prozessorkern/LedPixel/stm32f030/pcb/led_pixel_stm32f030/doc/led_pixel_stm32f030.pdf

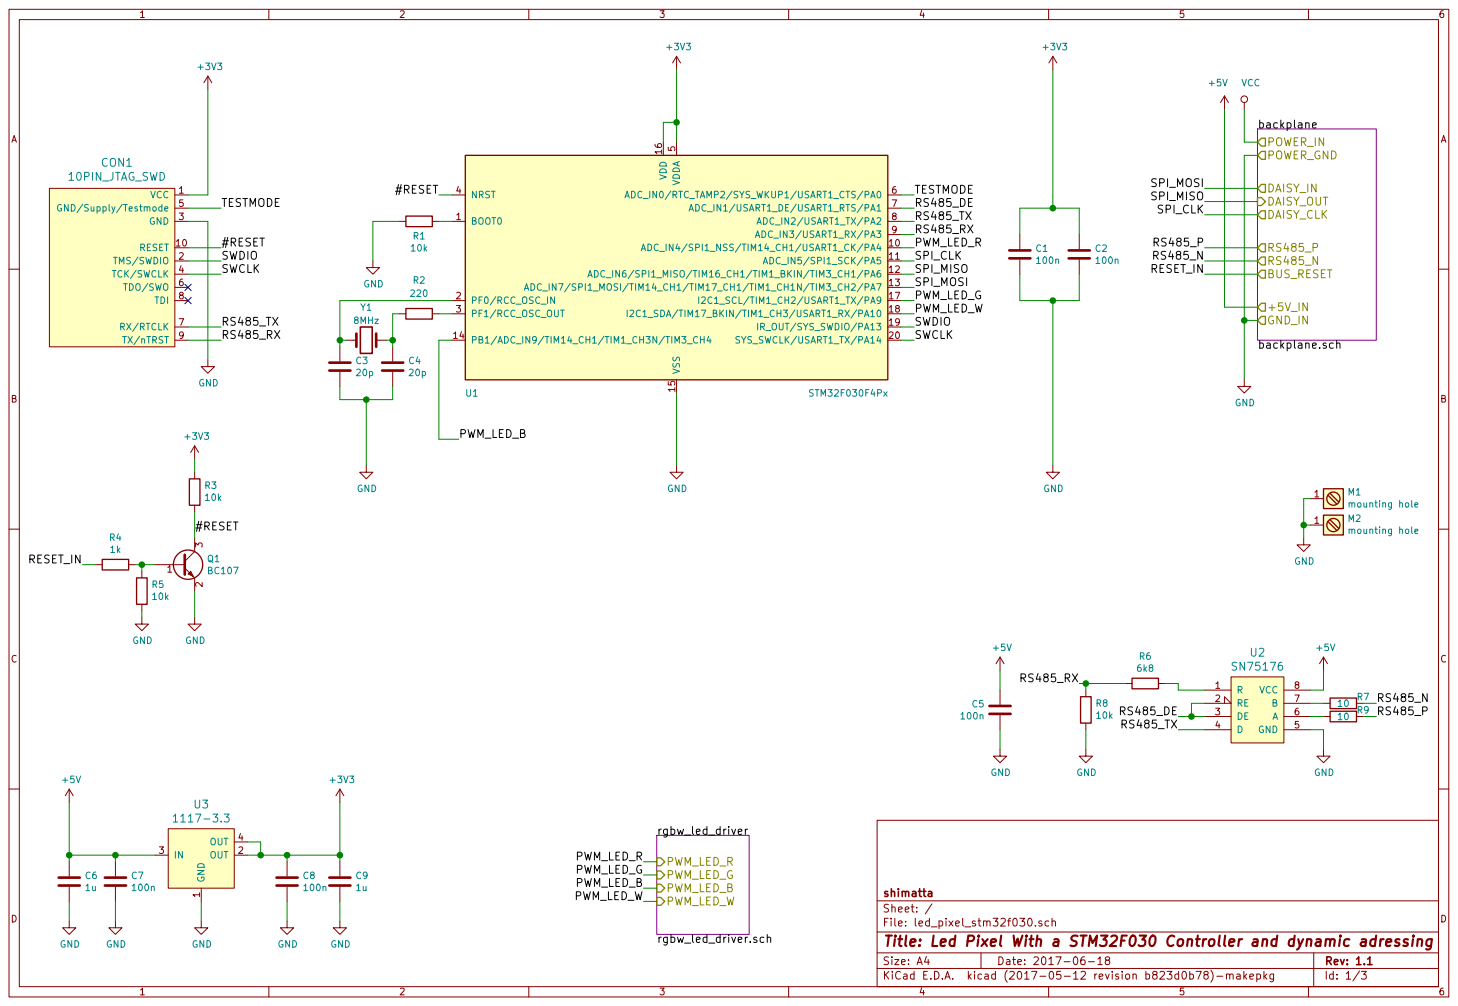
[picture p6: page 1]

File: led_pixel_stm32f030.sch Sheet: / shimatta C7

Id: 1/3 Title: Led Pixel With a STM32F030 Controller and dynamic adressing

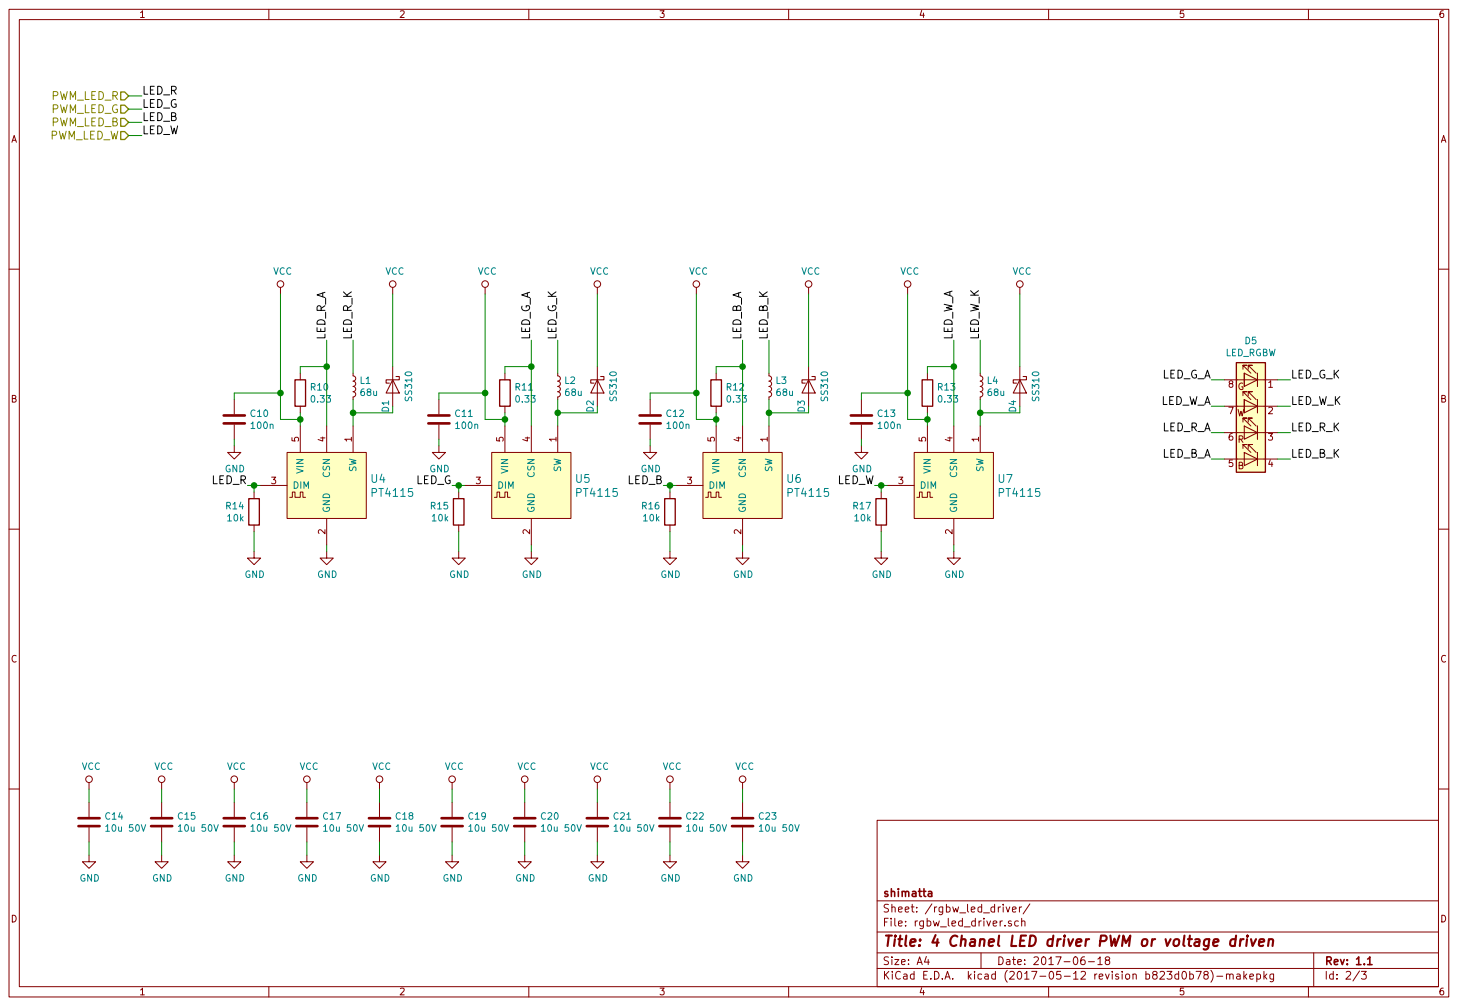
[picture p7: page 2]

File: rgbw_led_driver.sch
Id: 2/3 Title: 4 Chanel LED driver PWM or voltage driven

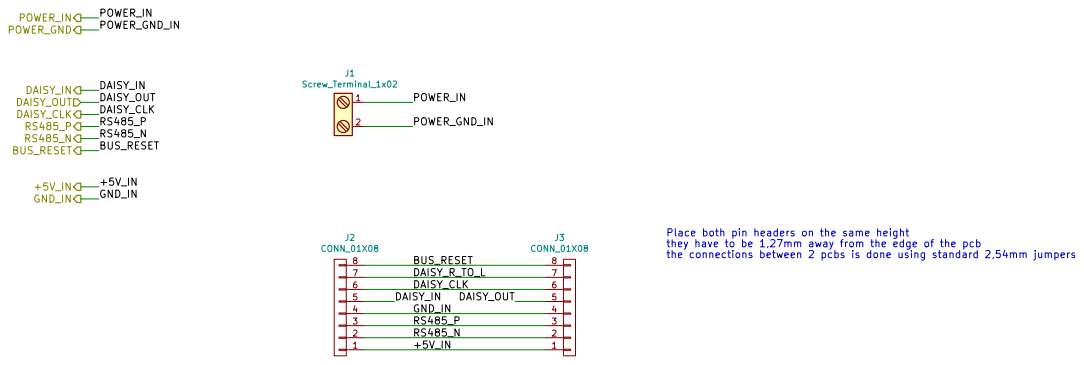
[picture p8: page 3]

Place both pin headers on the same height
they have to be 1,27mm away from the edge of the pcb
the connections between 2 pcbs is done using standard 2,54mm jumpers

File: backplane.sch
Id: 3/3 Title: Led Pixel Backplane connection
