prozessorkern/LedPixel/atmega8/pcb/led_pixel/doc/led_pixel.pdf

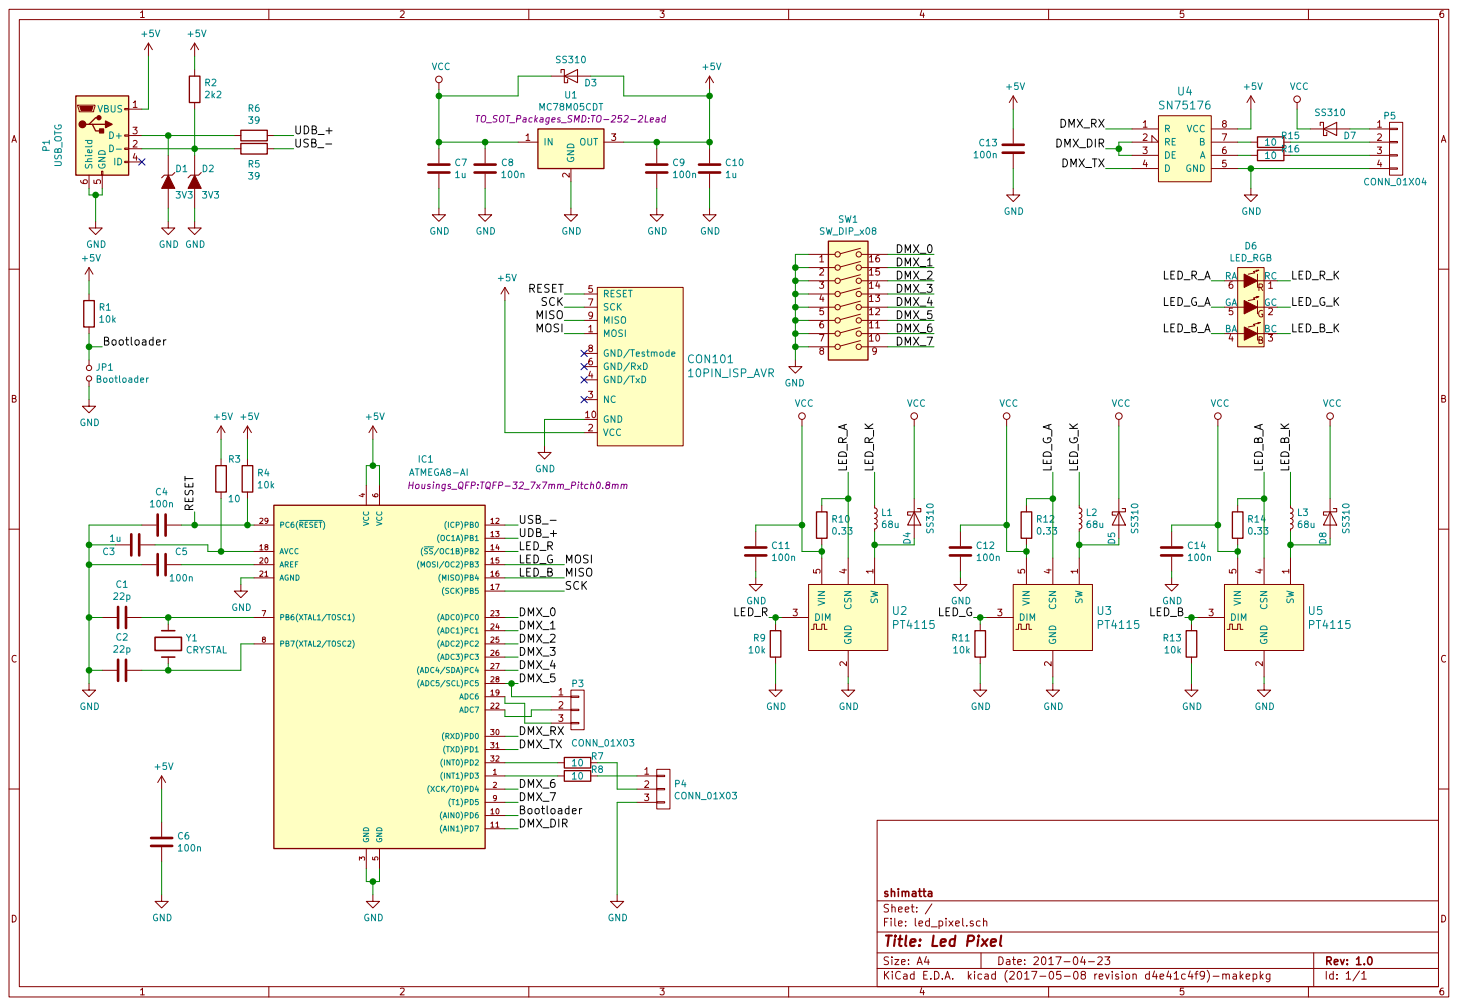
[picture p9: page 1]

UDB_+ Bootloader Bootloader JP1 Bootloader GND

File: led_pixel.sch Sheet: / shimatta

Id: 1/1 Title: Led Pixel
