prozessorkern/LedPixel/stm32f030/pcb/led_pixel_stm32f030/x4/doc/led_pixel_stm32f030_x4-B_SilkS.pdf

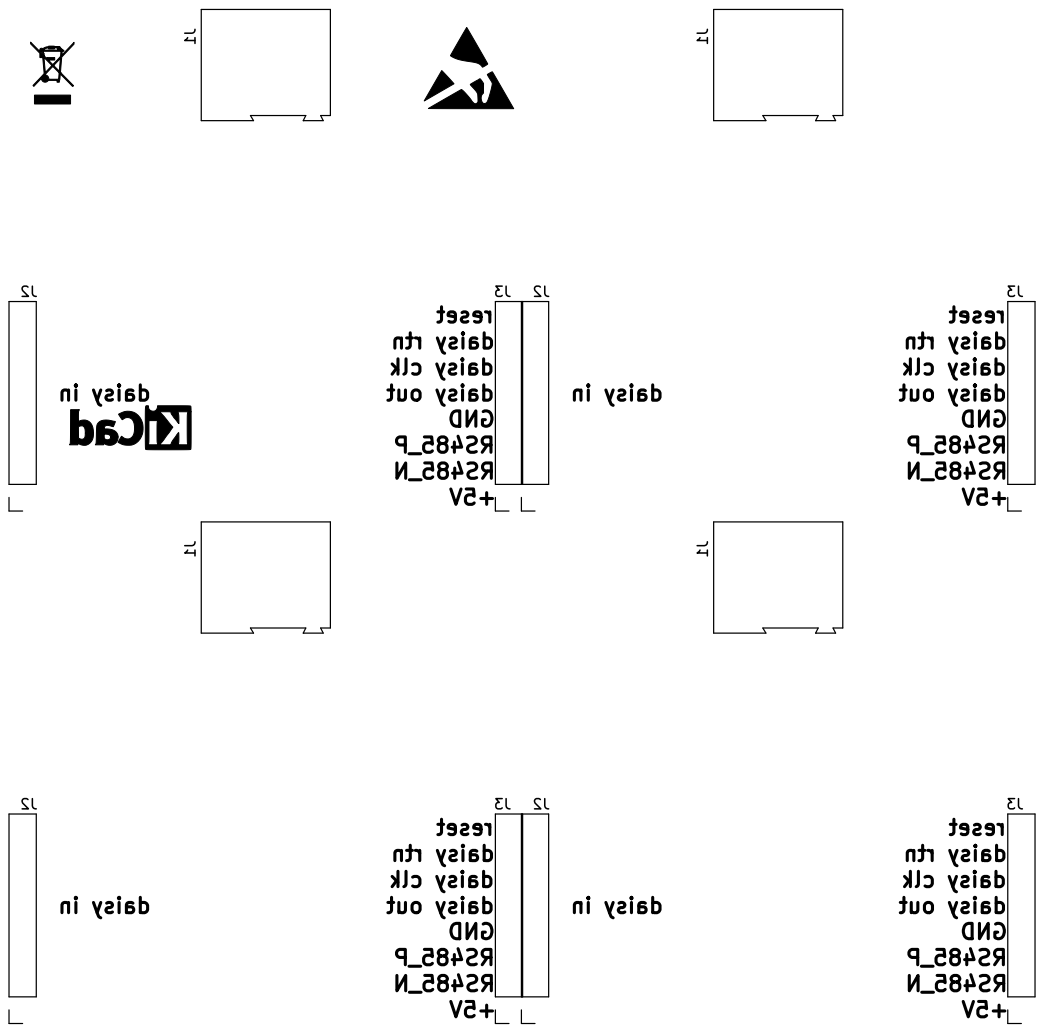
[picture p10: page 1]

daisy out daisy out +5V RS485_N

daisy out reset daisy rtn
