prozessorkern/LedPixel/stm32f030/pcb/led_pixel_stm32f030/doc/led_pixel_stm32f030-B.Cu.pdf

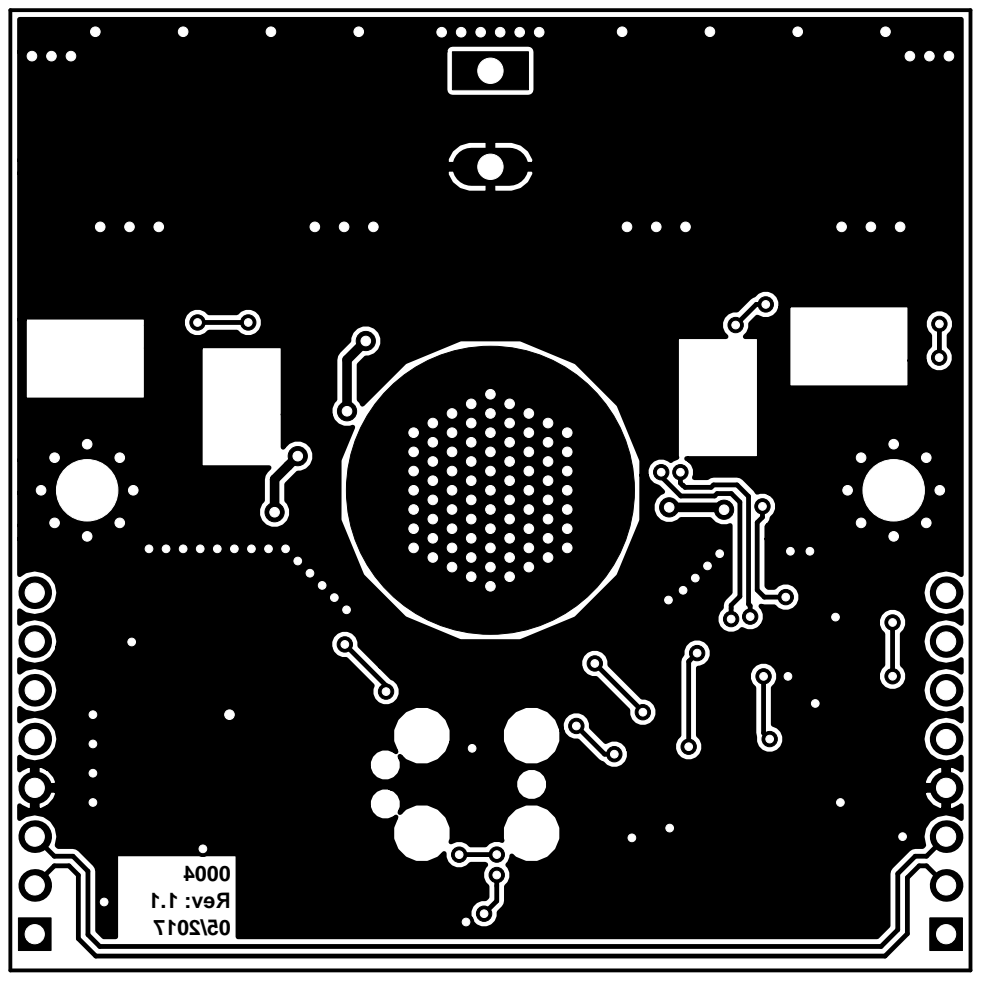
[picture p20: page 1]
