prozessorkern/LedPixel/stm32f030/pcb/led_pixel_stm32f030/doc/led_pixel_stm32f030-B.Mask.pdf

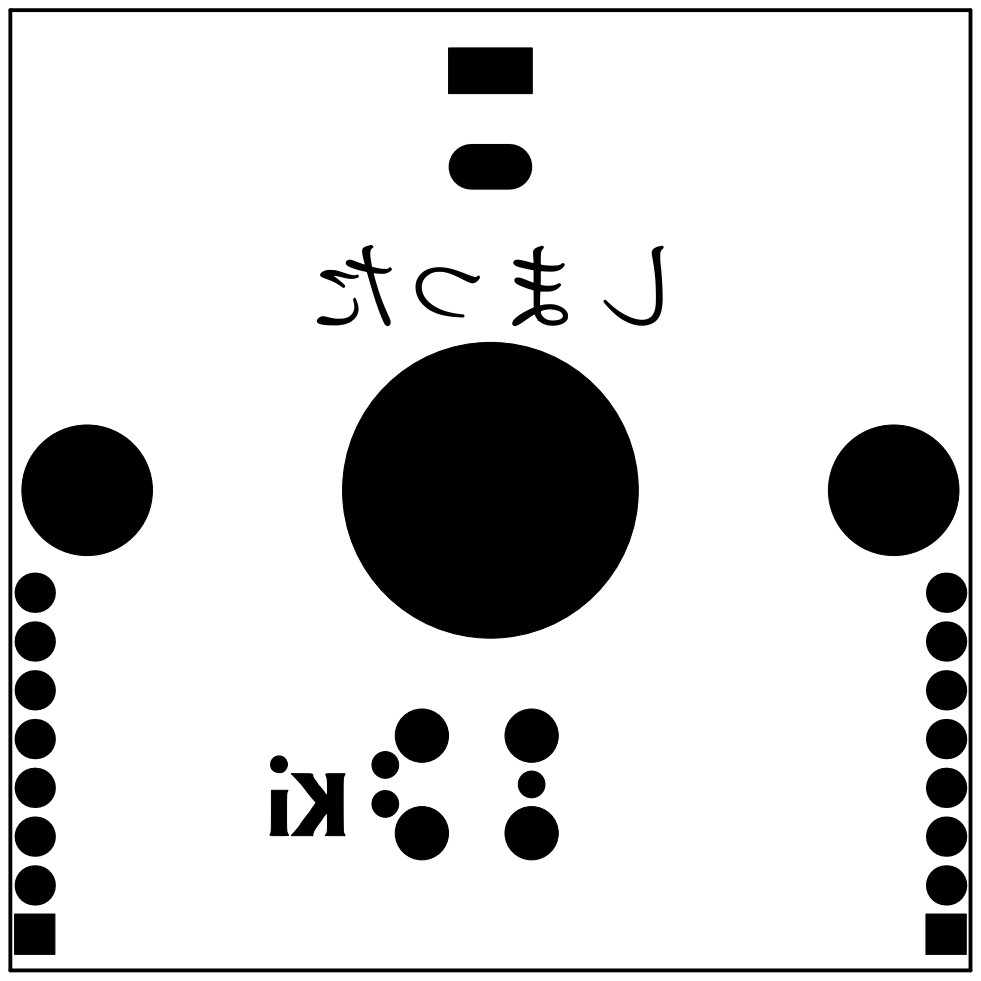
[picture p21: page 1]
