prozessorkern/LedPixel/stm32f030/pcb/led_pixel_stm32f030/doc/led_pixel_stm32f030-B.SilkS.pdf

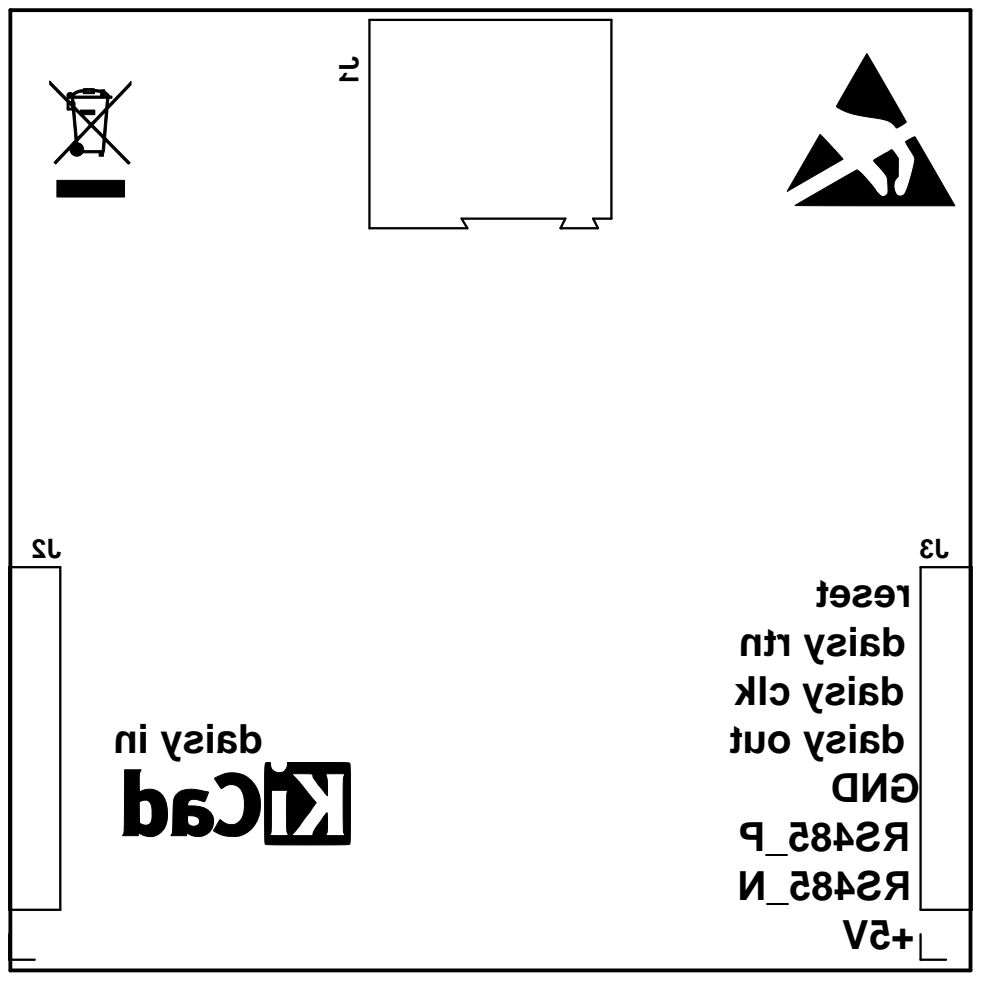
[picture p22: page 1]
