prozessorkern/LedPixel/stm32f030/pcb/led_pixel_stm32f030/doc/led_pixel_stm32f030-F.Cu.pdf

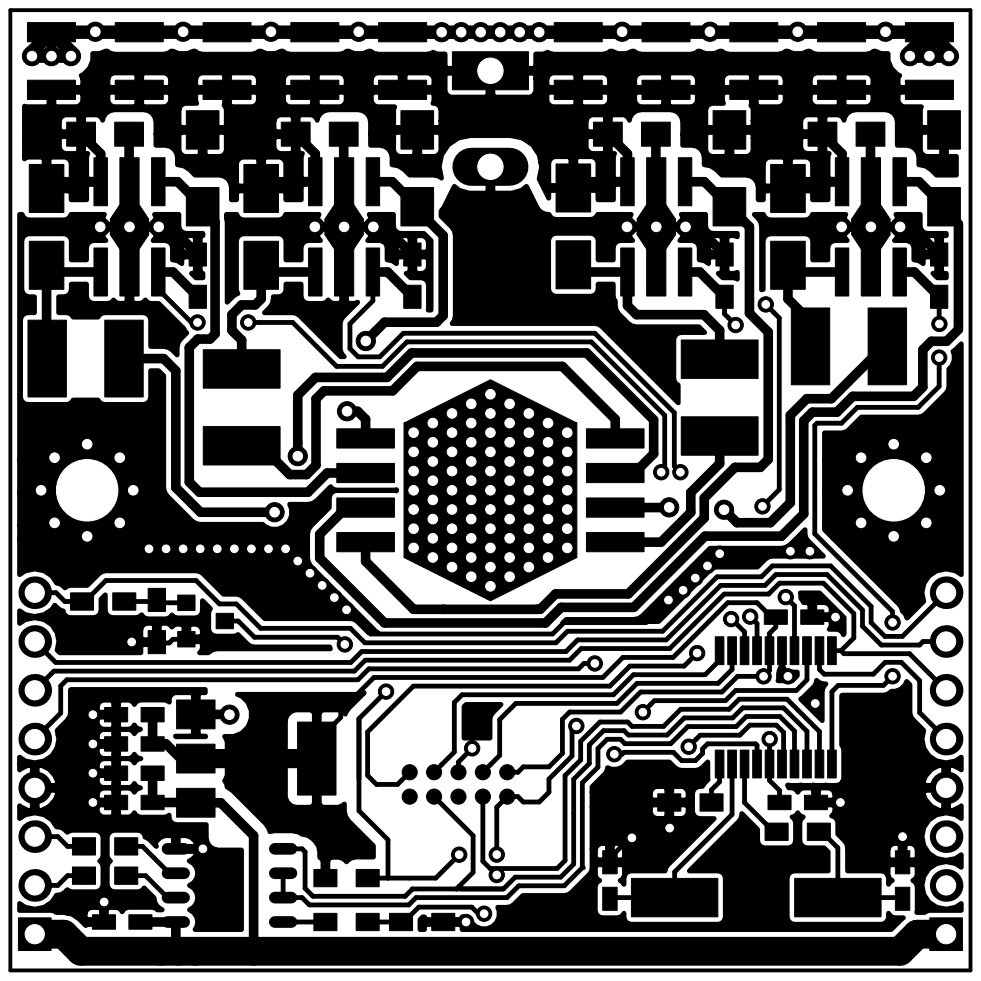
[picture p23: page 1]
