prozessorkern/LedPixel/stm32f030/pcb/led_pixel_stm32f030/doc/led_pixel_stm32f030-F.Mask.pdf

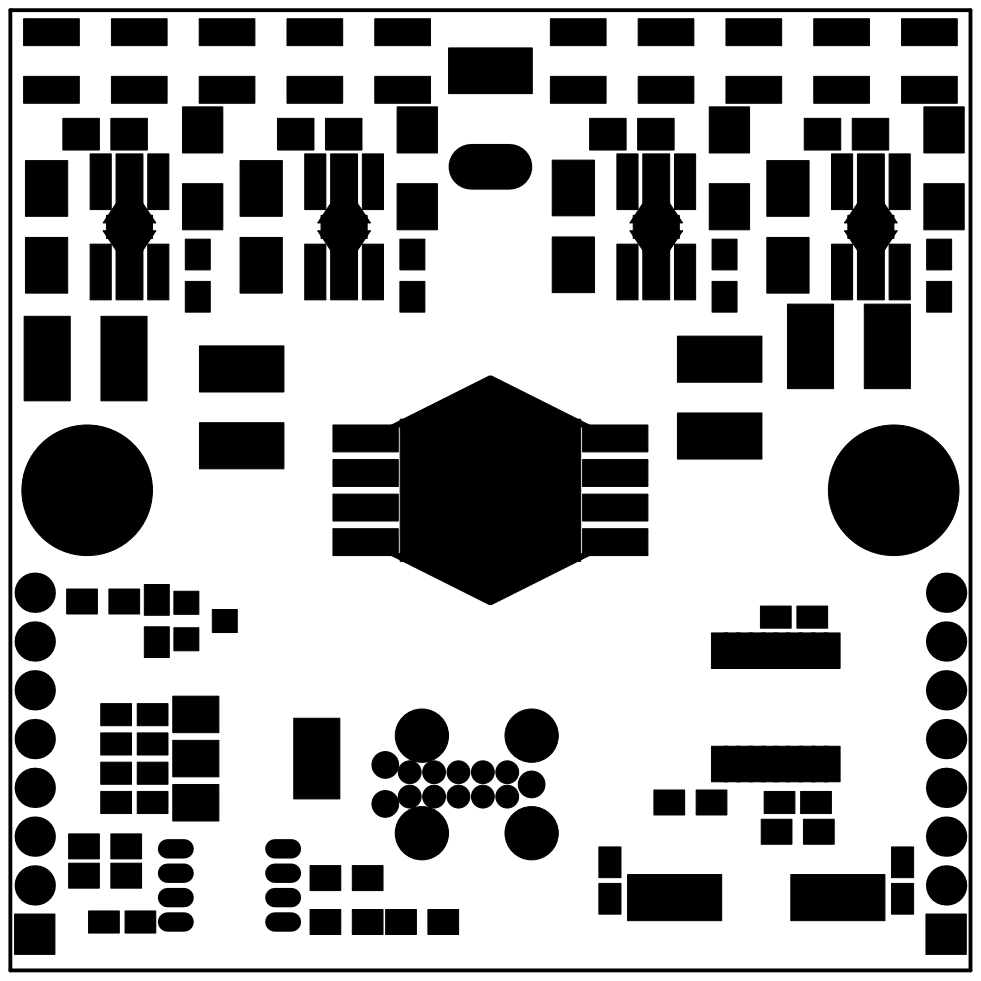
[picture p24: page 1]
