prozessorkern/LedPixel/stm32f030/pcb/led_pixel_stm32f030/doc/led_pixel_stm32f030-F.Paste.pdf

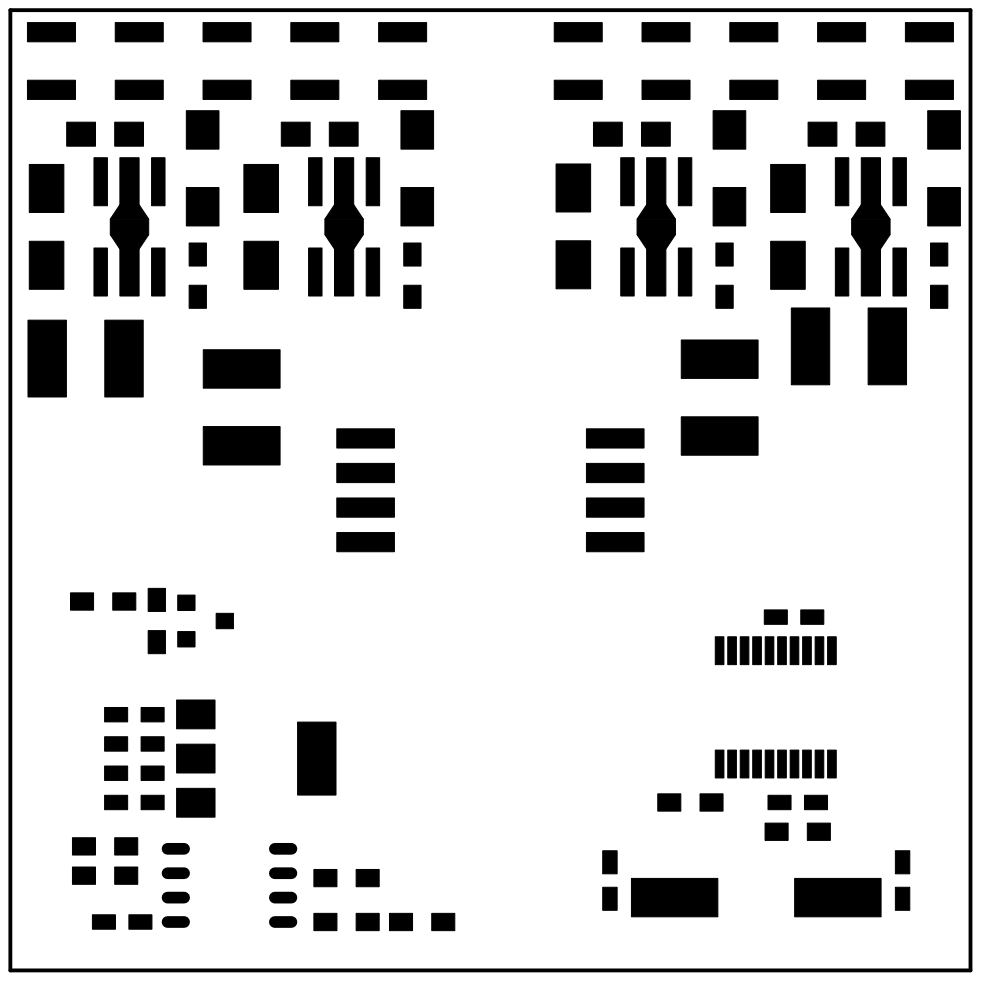
[picture p25: page 1]
