prozessorkern/LedPixel/stm32f030/pcb/led_pixel_stm32f030/doc/led_pixel_stm32f030-F.SilkS.pdf

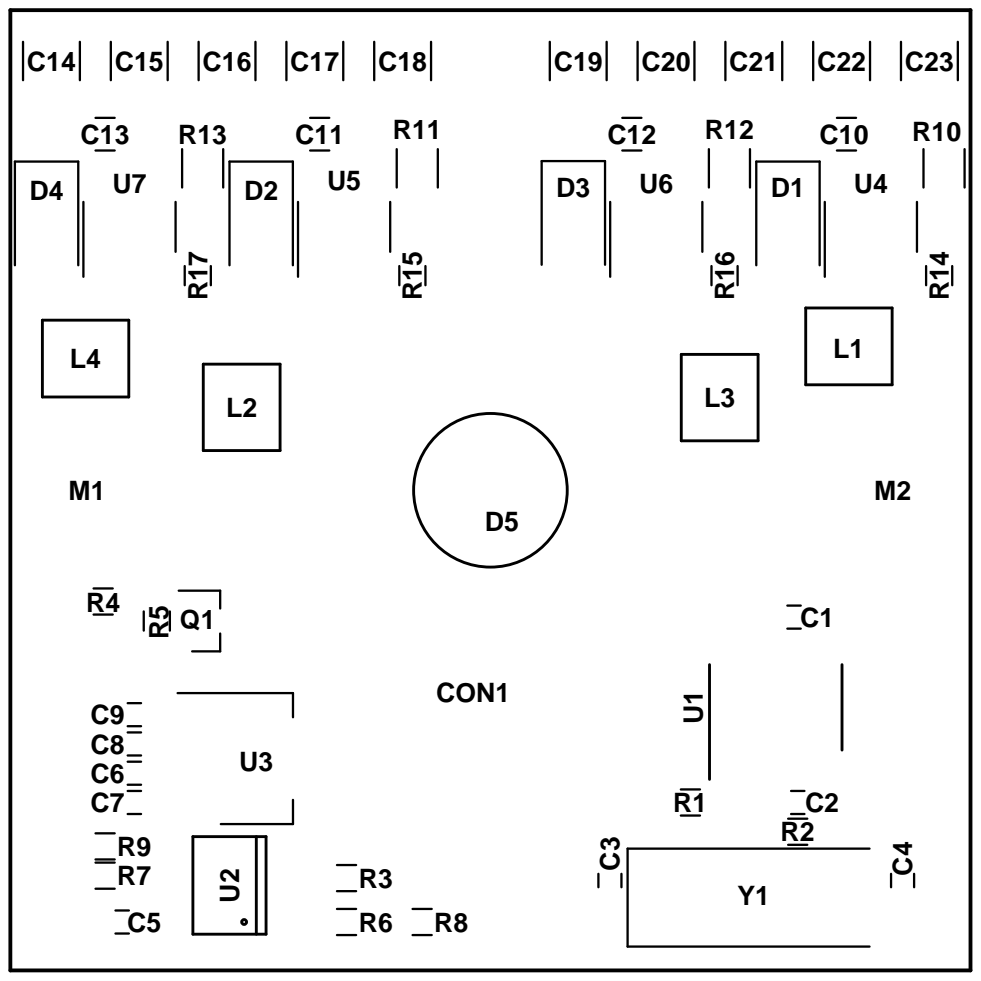
[picture p26: page 1]
