prozessorkern/LedPixel/atmega8/pcb/led_pixel/doc/led_pixel-B.Cu.pdf

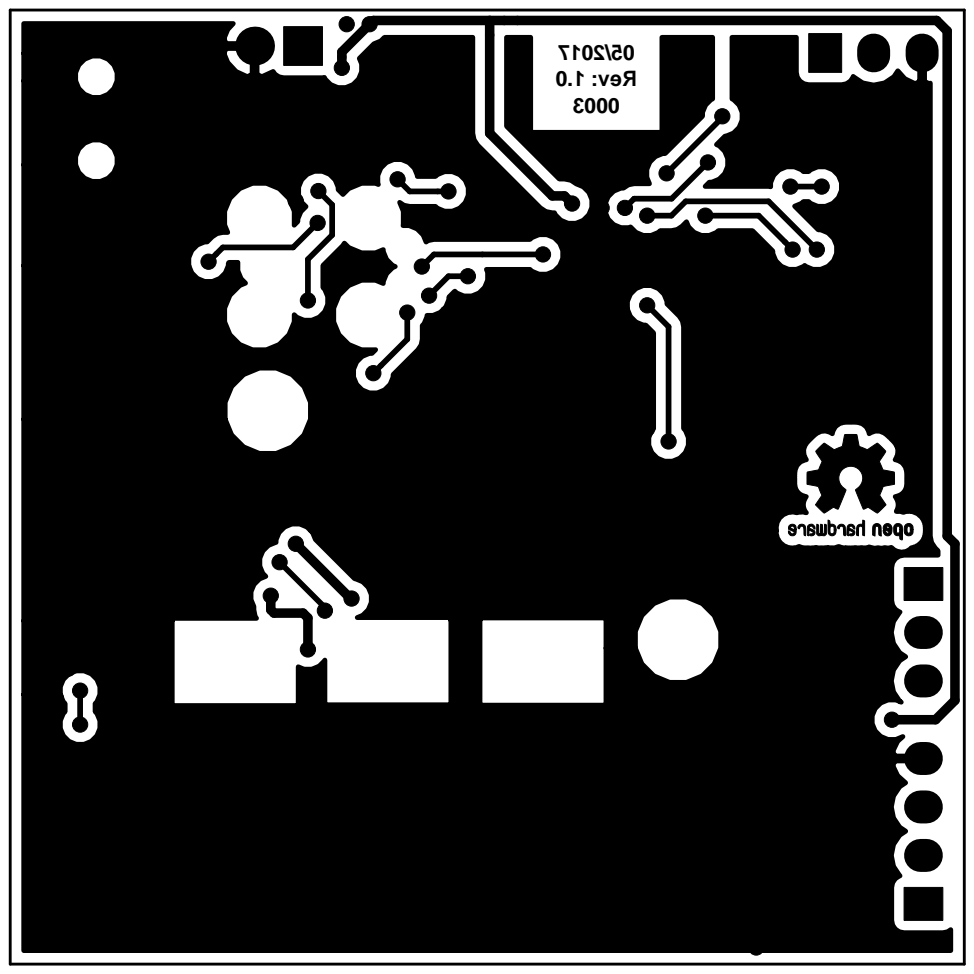
[picture p27: page 1]
