prozessorkern/LedPixel/atmega8/pcb/led_pixel/doc/led_pixel-B.Mask.pdf

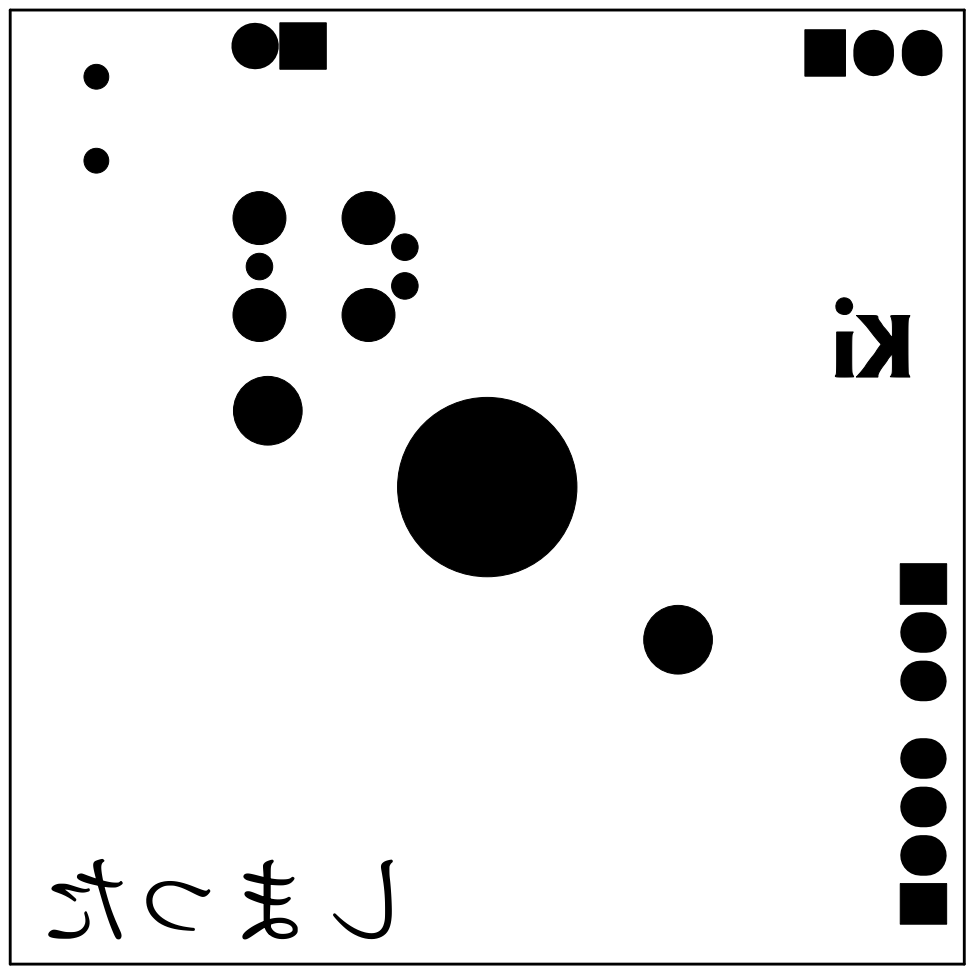
[picture p28: page 1]
