prozessorkern/LedPixel/atmega8/pcb/led_pixel/doc/led_pixel-B.Paste.pdf

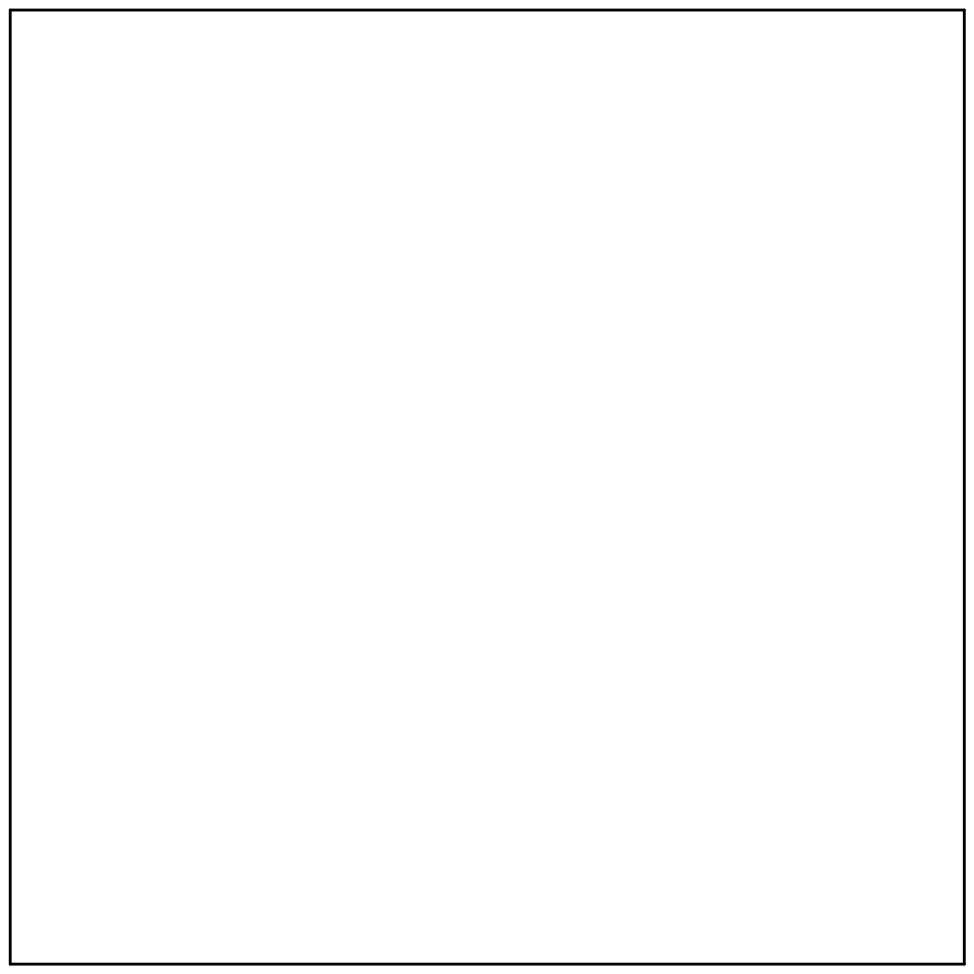
[picture p29: page 1]
