prozessorkern/LedPixel/atmega8/pcb/led_pixel/doc/led_pixel-B.SilkS.pdf

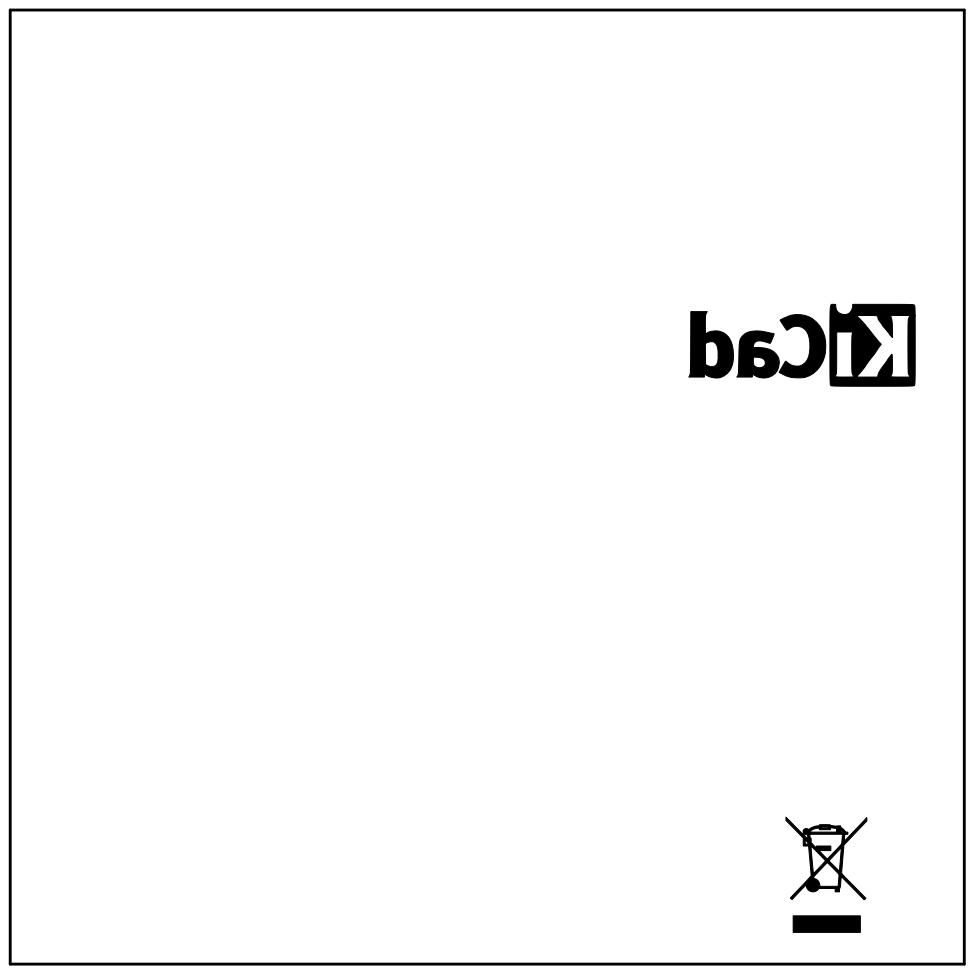
[picture p30: page 1]
