prozessorkern/LedPixel/atmega8/pcb/led_pixel/doc/led_pixel-F.Cu.pdf

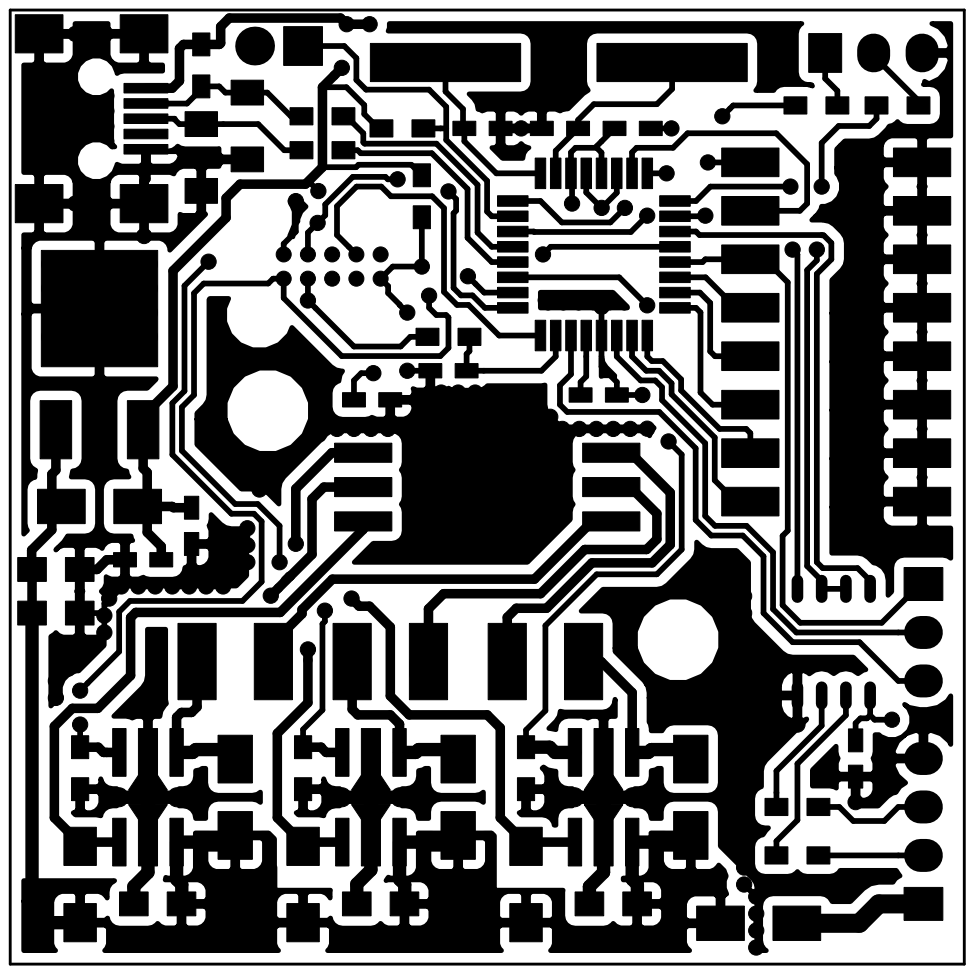
[picture p31: page 1]
