prozessorkern/LedPixel/atmega8/pcb/led_pixel/doc/led_pixel-F.Mask.pdf

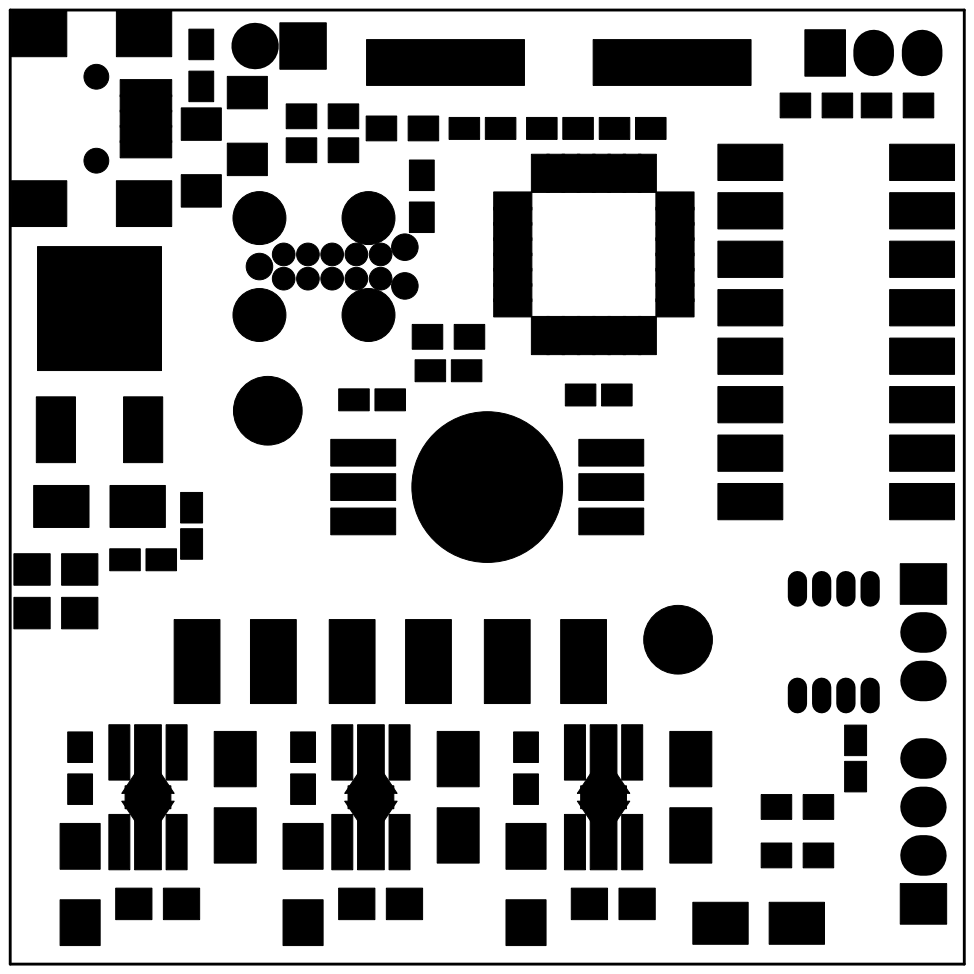
[picture p32: page 1]
