prozessorkern/LedPixel/atmega8/pcb/led_pixel/doc/led_pixel-F.Paste.pdf

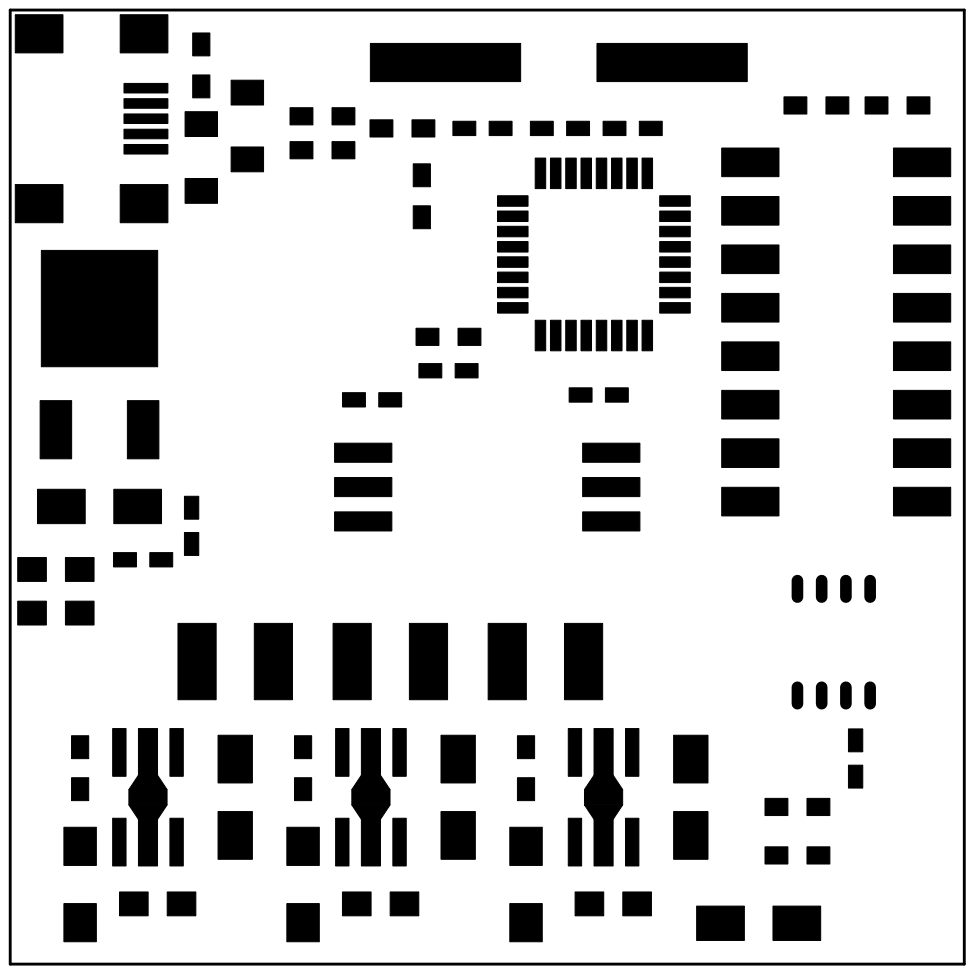
[picture p33: page 1]
