prozessorkern/LedPixel/atmega8/pcb/led_pixel/doc/led_pixel-F.SilkS.pdf

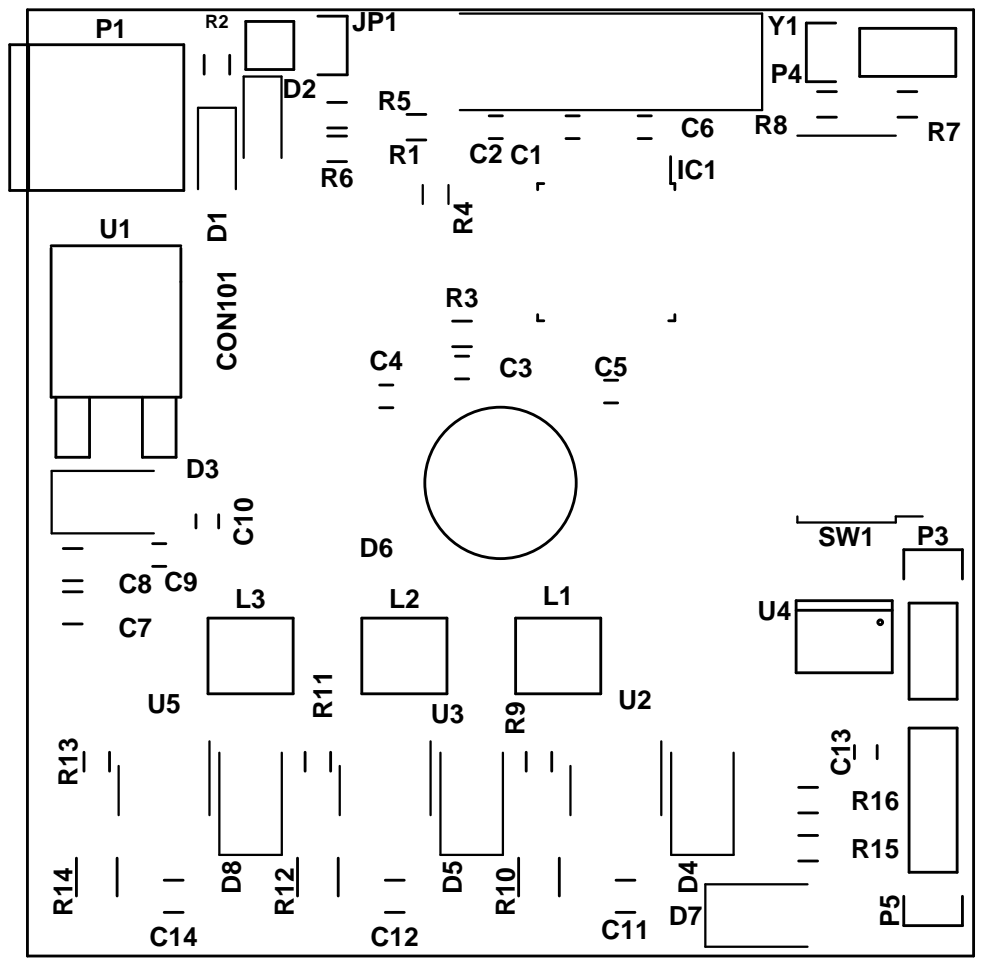
[picture p34: page 1]
