prozessorkern/LedPixel/stm32f030/pcb/led_pixel_stm32f030/x4/doc/led_pixel_stm32f030_x4-B_Cu.pdf

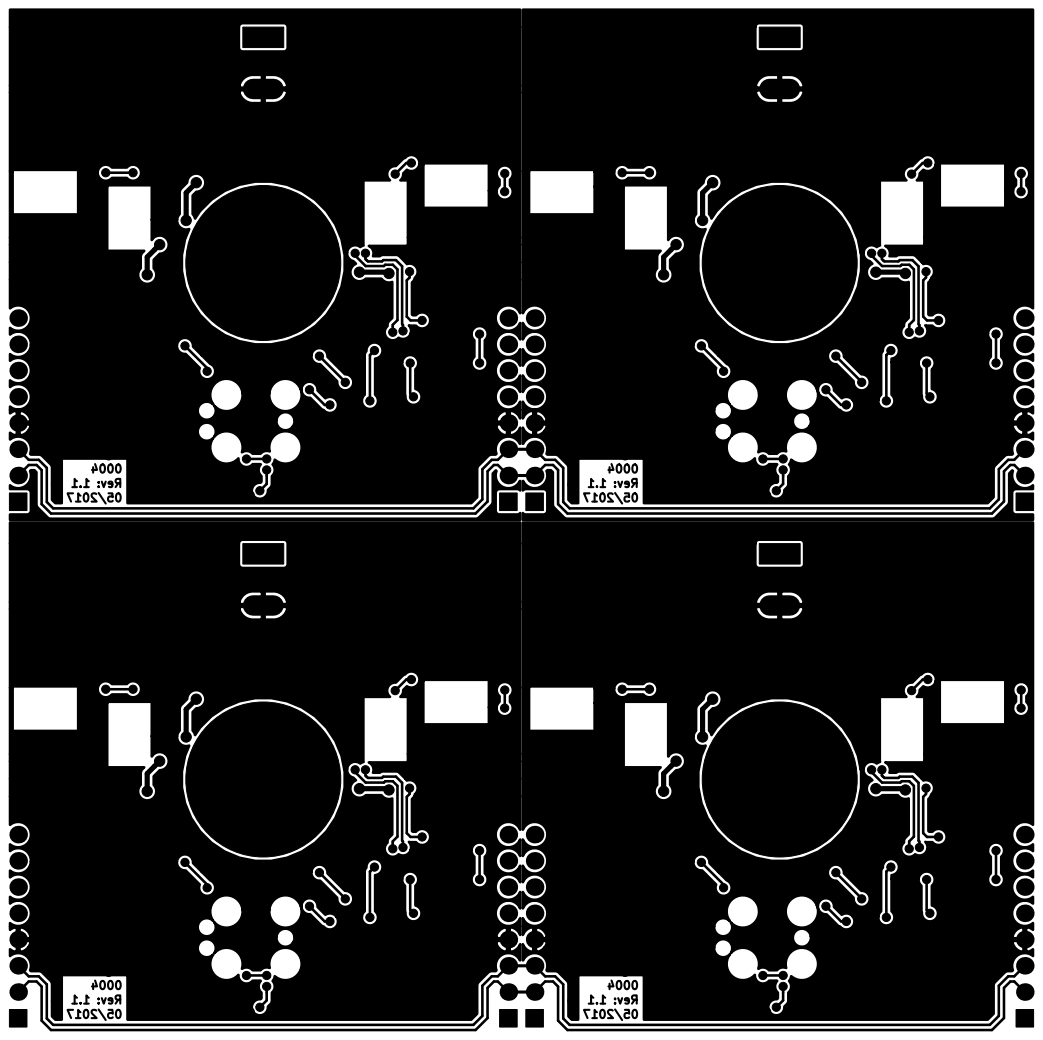
[picture p35: page 1]
