prozessorkern/LedPixel/stm32f030/pcb/led_pixel_stm32f030/x4/doc/led_pixel_stm32f030_x4-B_Mask.pdf

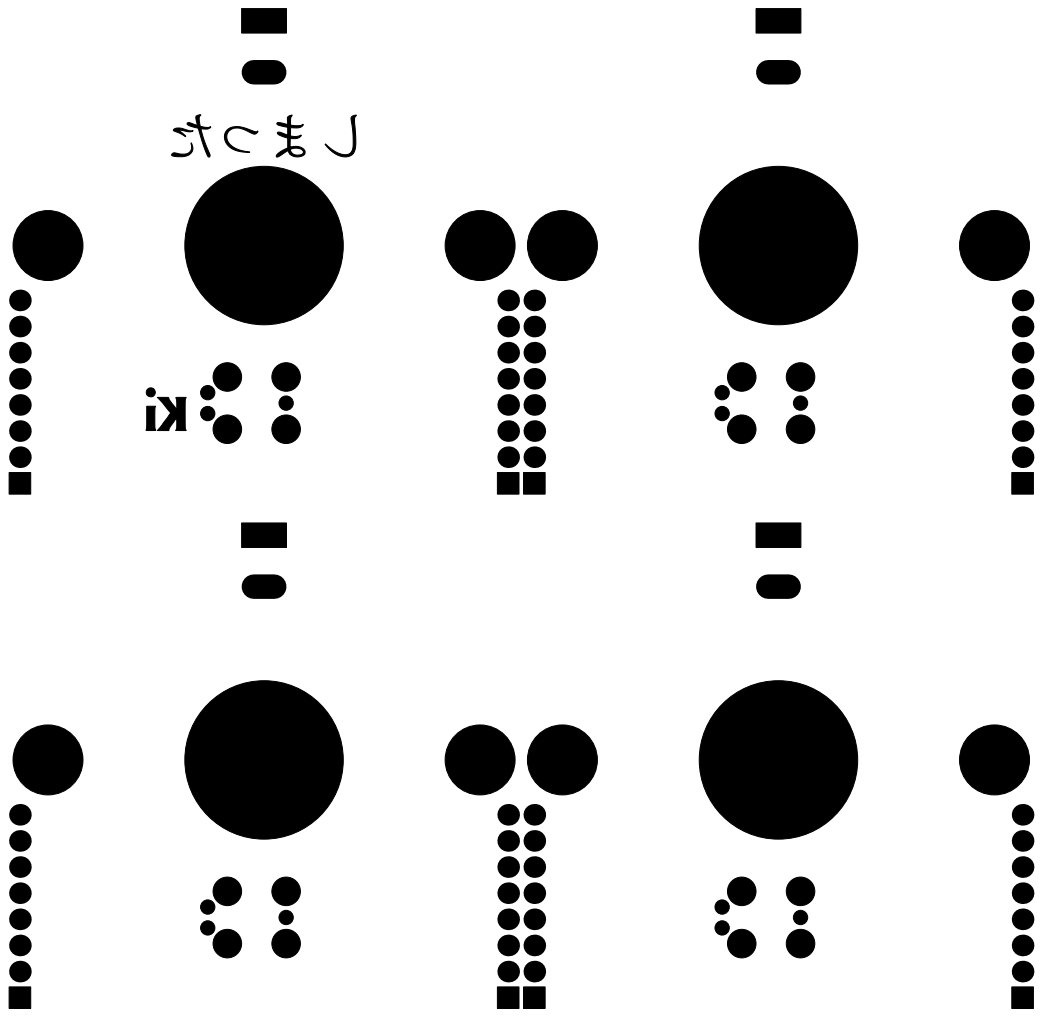
[picture p36: page 1]
